gkasprow/Sensor-Box/Sensor_Box_Hardware/Sensor-Box/Sensor_Box_Hub/ATSAMD9.PNG

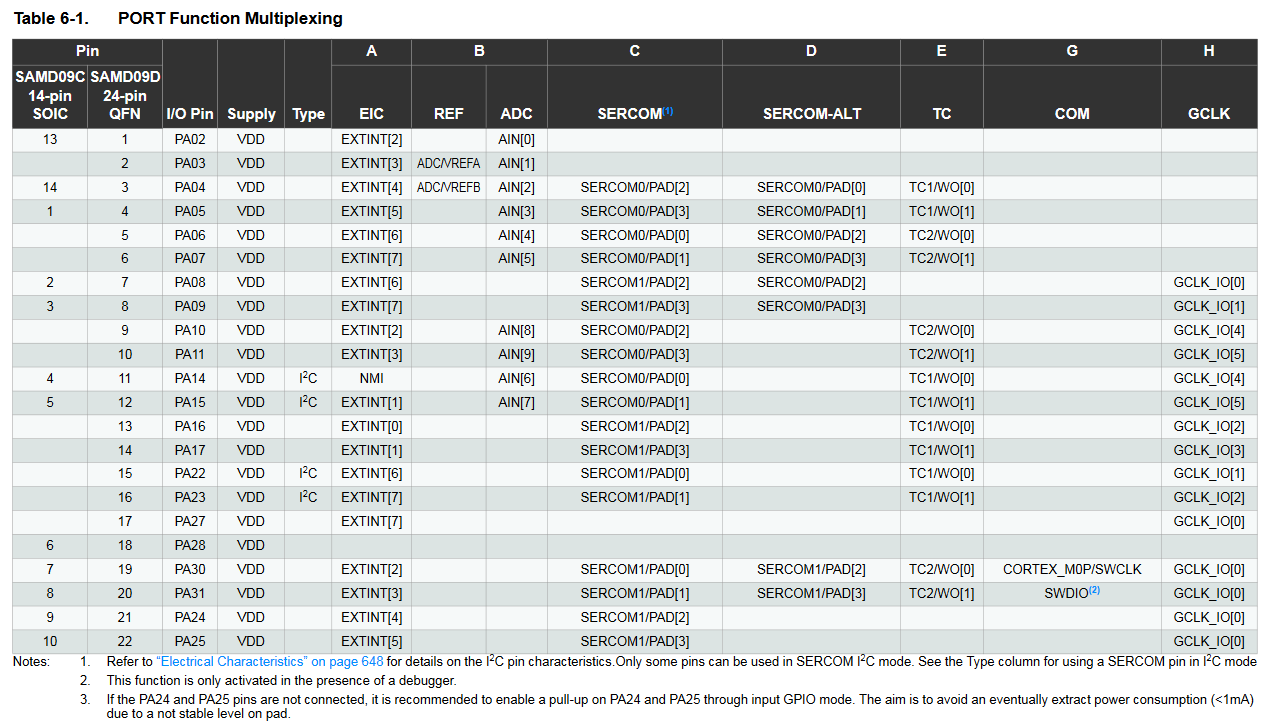
Sensor_Box_Hardware/Sensor-Box/Sensor_Box_Hub/ATSAMD9.PNG
