gkasprow/Sensor-Box/Sensor_Box_Hardware/Sensor-Box/Sensor_Box_Hub/ESP32-1.PNG

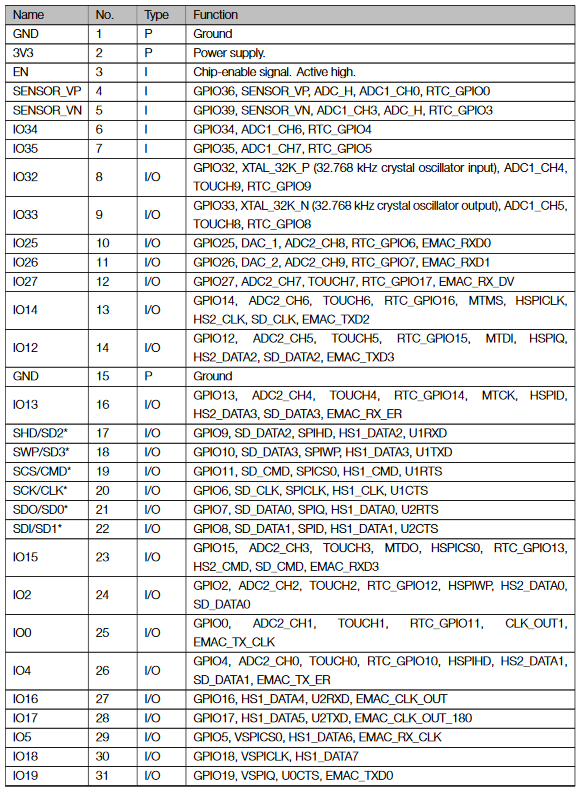
Sensor_Box_Hardware/Sensor-Box/Sensor_Box_Hub/ESP32-1.PNG
