gkasprow/Sensor-Box/Sensor_Box_Hardware/Sensor-Box/Sensor_Box_Hub_SAMD21/ATSAMD21a.PNG

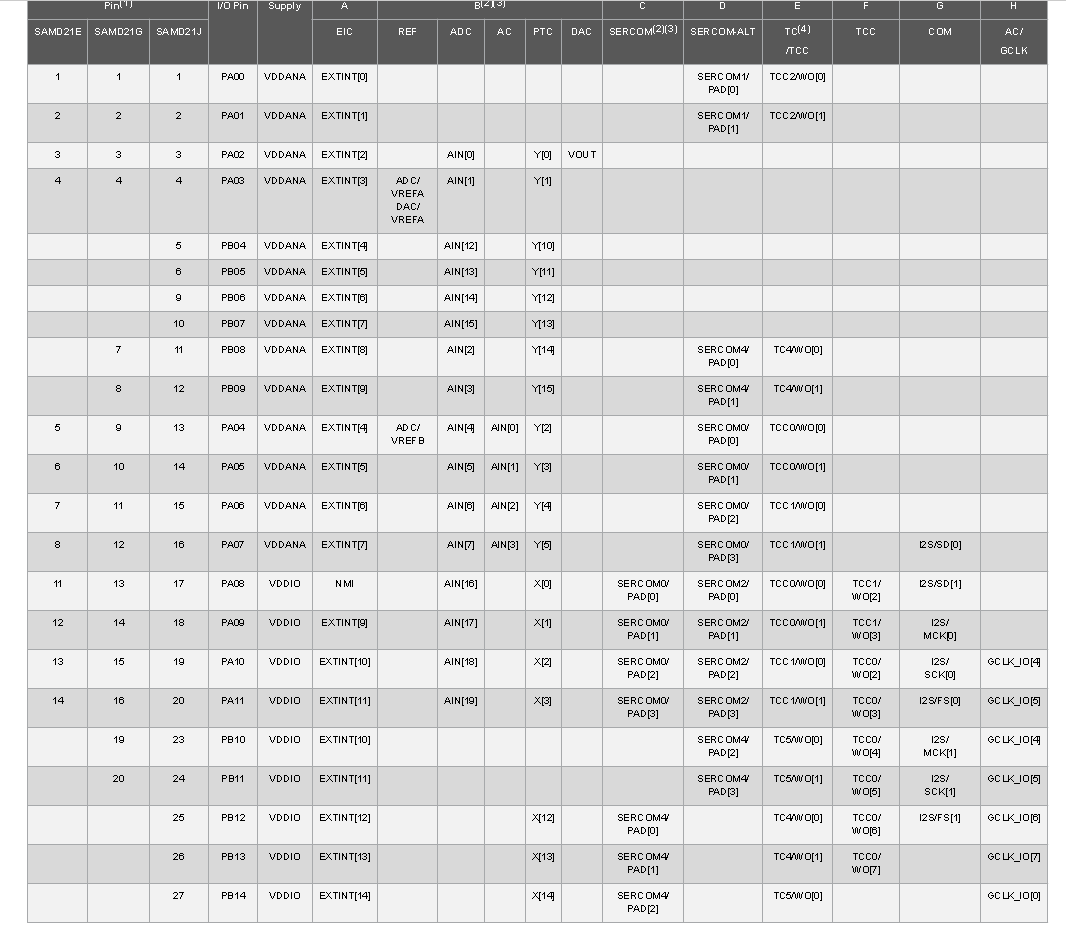
Sensor_Box_Hardware/Sensor-Box/Sensor_Box_Hub_SAMD21/ATSAMD21a.PNG
