gkasprow/Sensor-Box/Sensor_Box_Hardware/Sensor-Box/Sensor_Box_PWR_Backup/LED_status.PNG

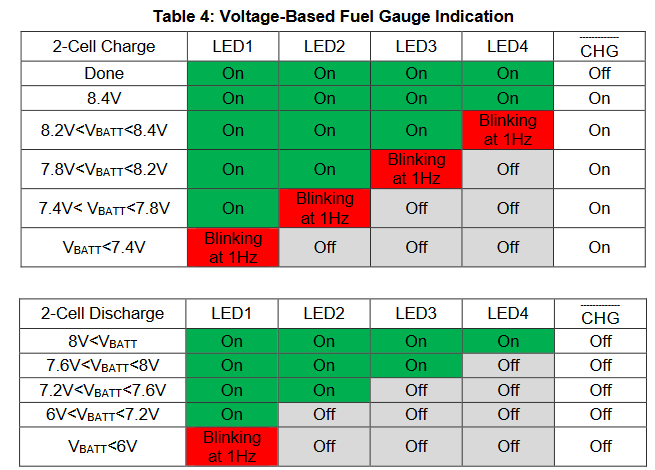
Sensor_Box_Hardware/Sensor-Box/Sensor_Box_PWR_Backup/LED_status.PNG
