gkasprow/Sensor-Box/MQTT_firmware/Stepper/Stepper/Stepper.ino

#include "credentials.h"
/*
 Stepper Motor Control - one revolution

 This program drives a unipolar or bipolar stepper motor.
 The motor is attached to digital pins 8 - 11 of the Arduino.

 The motor should revolve one revolution in one direction, then
 one revolution in the other direction.


 Created 11 Mar. 2007
 Modified 30 Nov. 2009
 by Tom Igoe

 */

#include <Stepper.h>

const int stepsPerRevolution = 1000;  // change this to fit the number of steps per revolution
// for your motor

// initialize the stepper library on pins 2 through 5:
Stepper myStepper(stepsPerRevolution, 2, 3, 4, 5);

void setup() {
  // set the speed at 60 rpm:
  myStepper.setSpeed(20);
  // initialize the serial port:
  Serial.begin(9600);
}

void loop() {
  // step one revolution  in one direction:
  Serial.println("clockwise");
  myStepper.step(stepsPerRevolution);
  delay(500);

  // step one revolution in the other direction:
  Serial.println("counterclockwise");
  myStepper.step(-stepsPerRevolution);
  delay(500);
}
